fgutep/MetalFunk/3DModels/Y-Axis/Y-Rod-Bracket_Front.stl

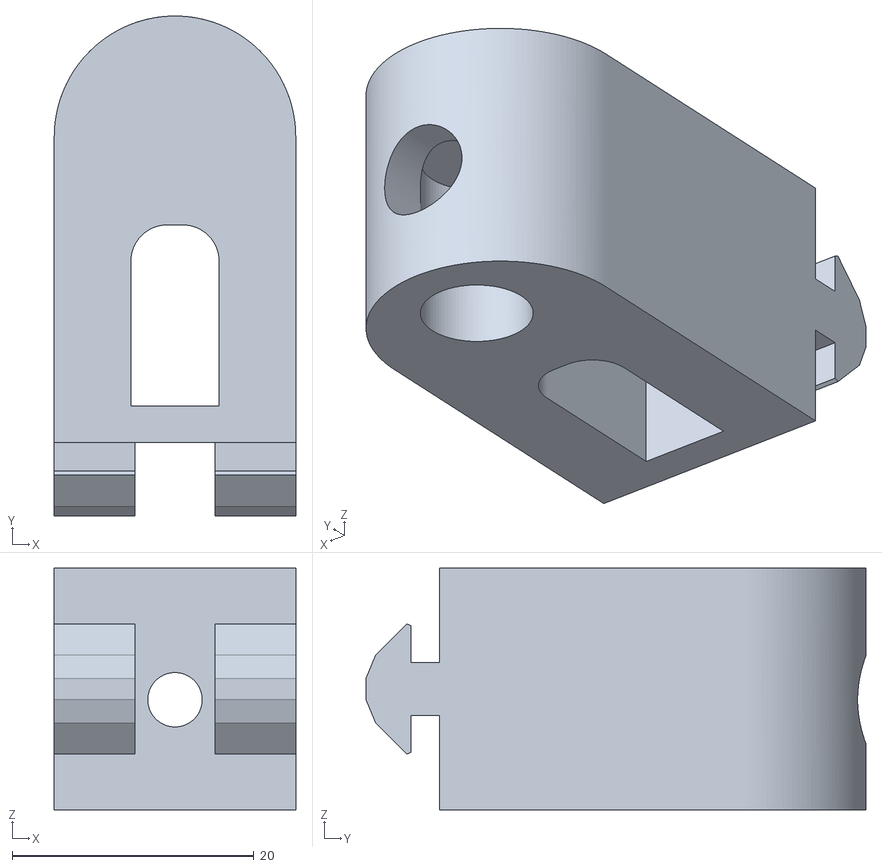
[picture p18: CAD file, 2024-07-13]
3DModels/Y-Axis/Y-Rod-Bracket_Front.stl
20.0 x 41.4 x 20.0
