fgutep/MetalFunk/3DModels/Y-Axis/Y-Belt-Idler.stl

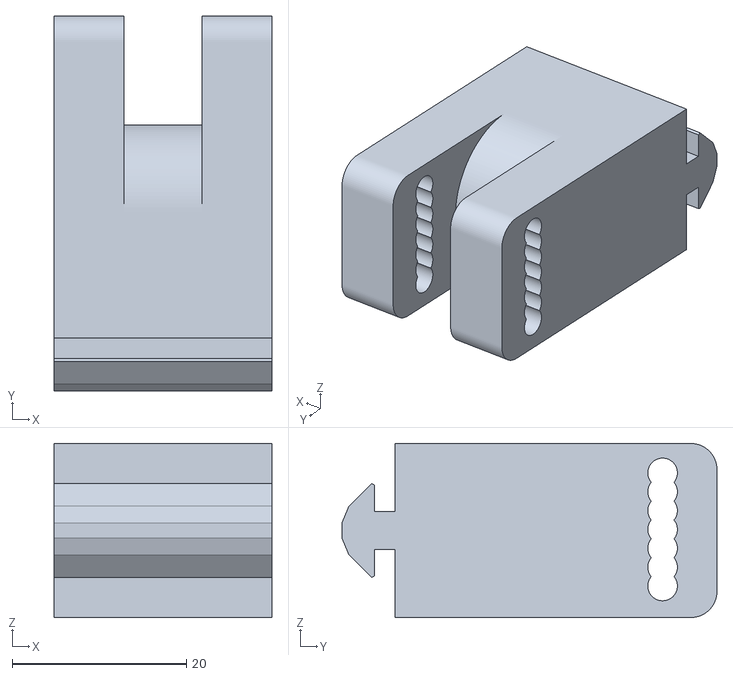
[picture p19: CAD file, 2024-07-13]
3DModels/Y-Axis/Y-Belt-Idler.stl
25.0 x 43.1 x 20.0
